SaLeeC/CentralElementForDipoleAntennaBNC/KiCad/AntenneCentraleDipoloStrumentato-Fronte.png

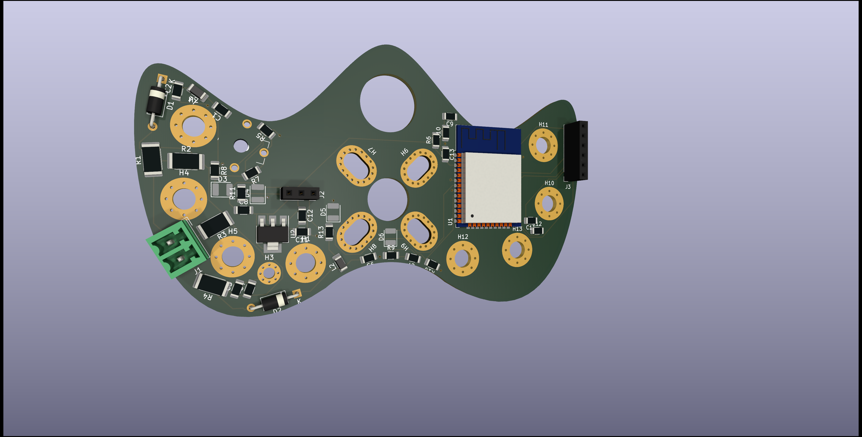
KiCad/AntenneCentraleDipoloStrumentato-Fronte.png
